Tonikiller10000/CH340G-FTDI-PROGRAMER/FtdiProgramer_Pictures/20230630_224606.jpg

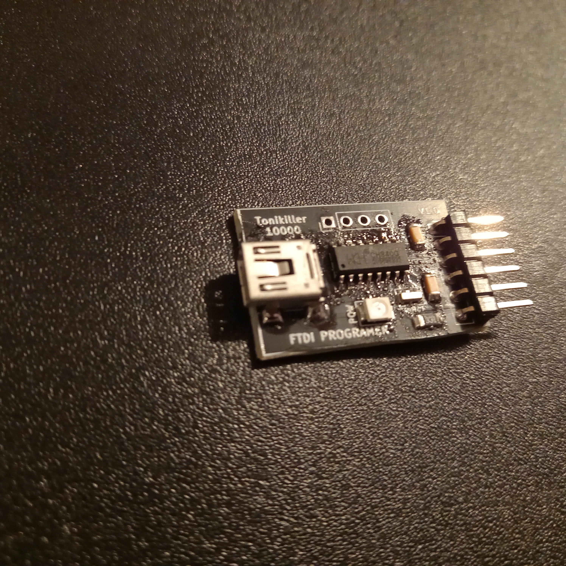
FtdiProgramer_Pictures/20230630_224606.jpg
