Tonikiller10000/CH340G-FTDI-PROGRAMER/FtdiProgramer_Pictures/20230701_103358.jpg

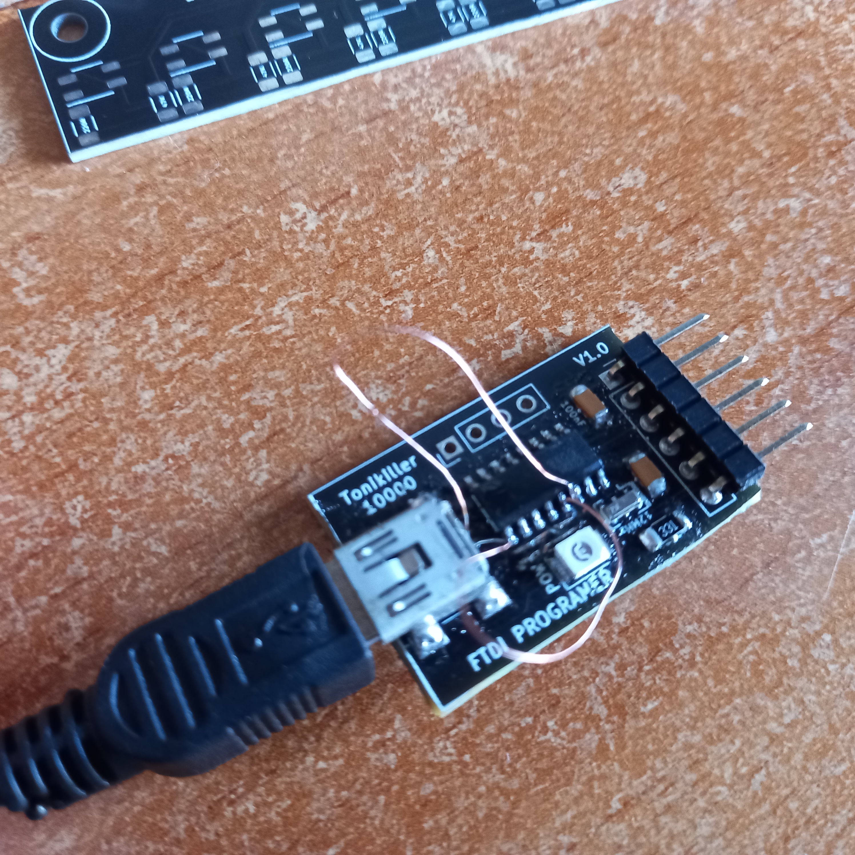
FtdiProgramer_Pictures/20230701_103358.jpg
