Tonikiller10000/CH340G-FTDI-PROGRAMER/FtdiProgramer_Pictures/20230709_143036.jpg

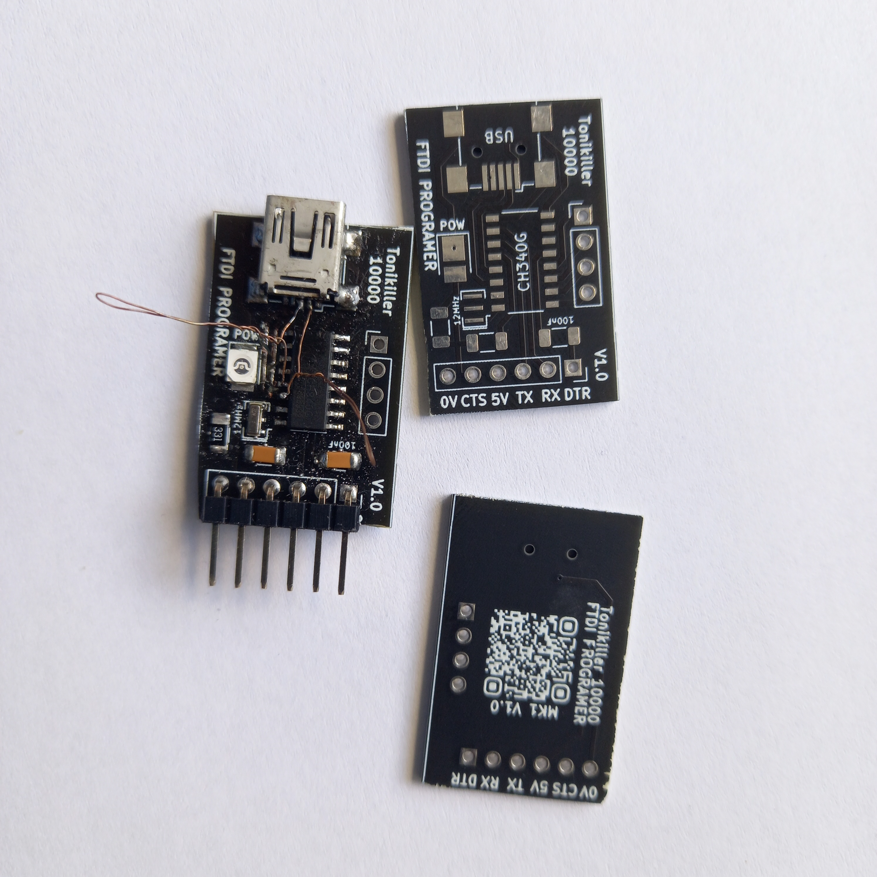
FtdiProgramer_Pictures/20230709_143036.jpg
