Tonikiller10000/CH340G-FTDI-PROGRAMER/FtdiProgramer_Pictures/20230709_143059.jpg

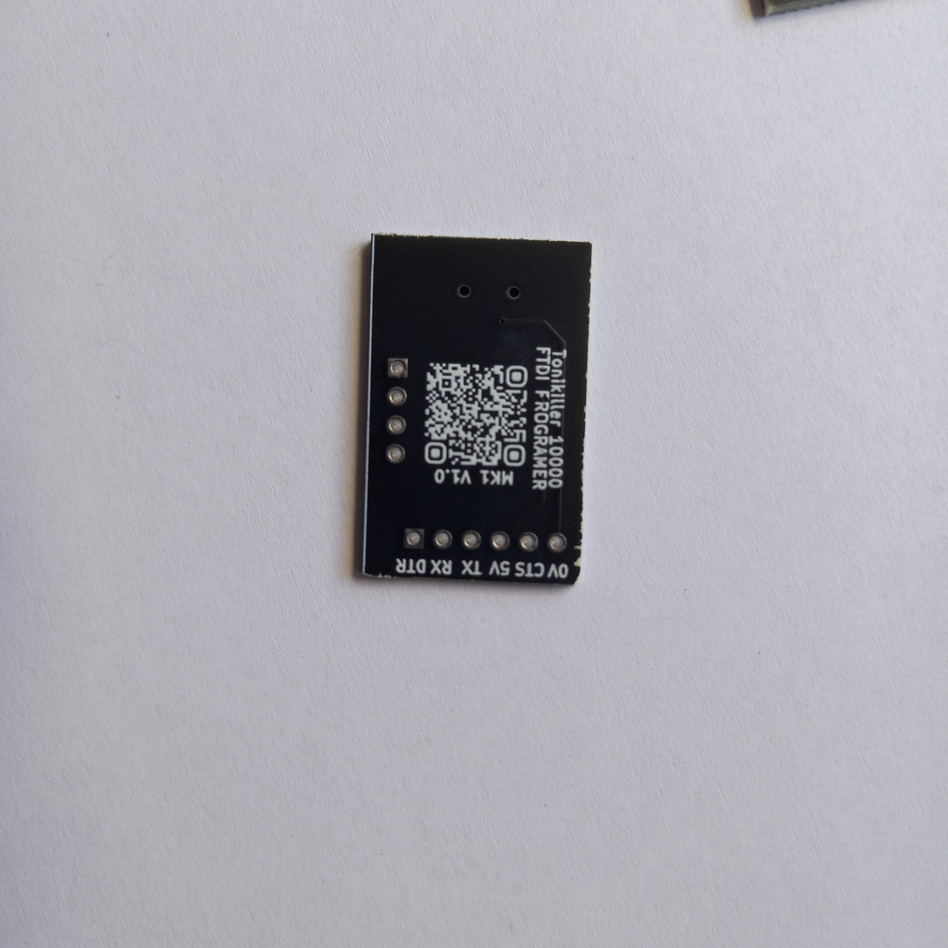
FtdiProgramer_Pictures/20230709_143059.jpg
