Tonikiller10000/CH340G-FTDI-PROGRAMER/FtdiProgramer_Pictures/20230709_143112.jpg

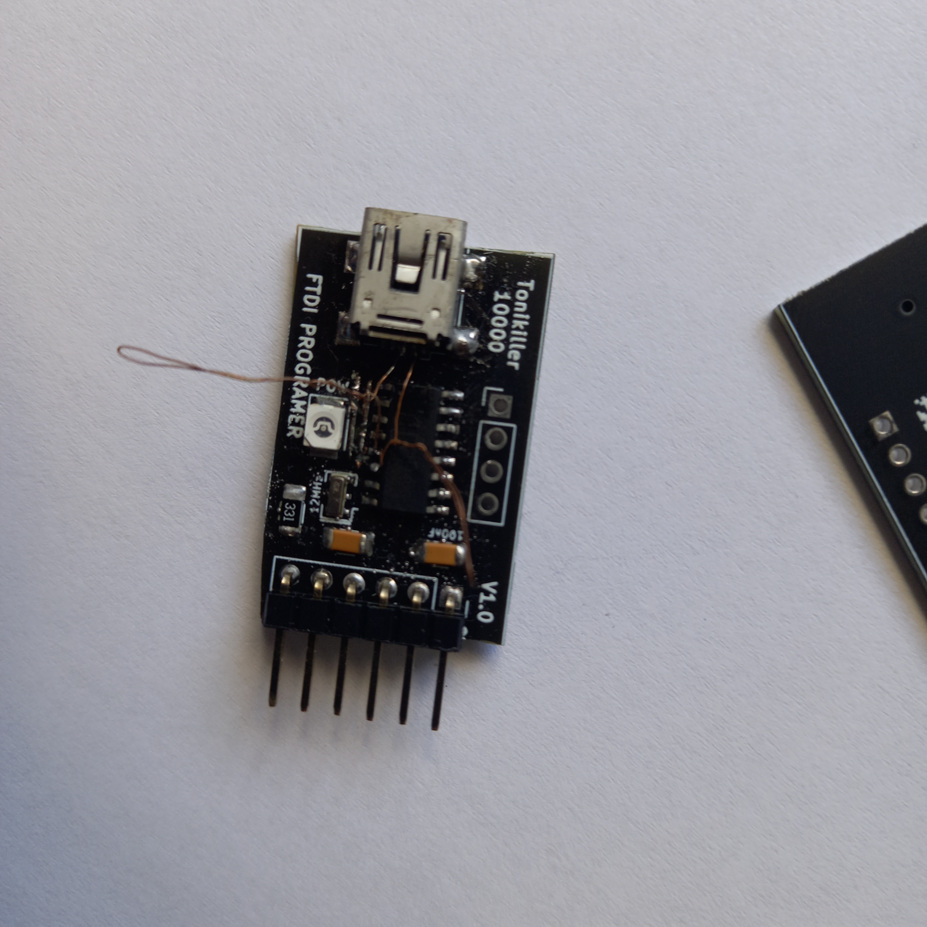
FtdiProgramer_Pictures/20230709_143112.jpg
