Tonikiller10000/CH340G-FTDI-PROGRAMER/FtdiProgramer_Pictures/20230920_141712.jpg

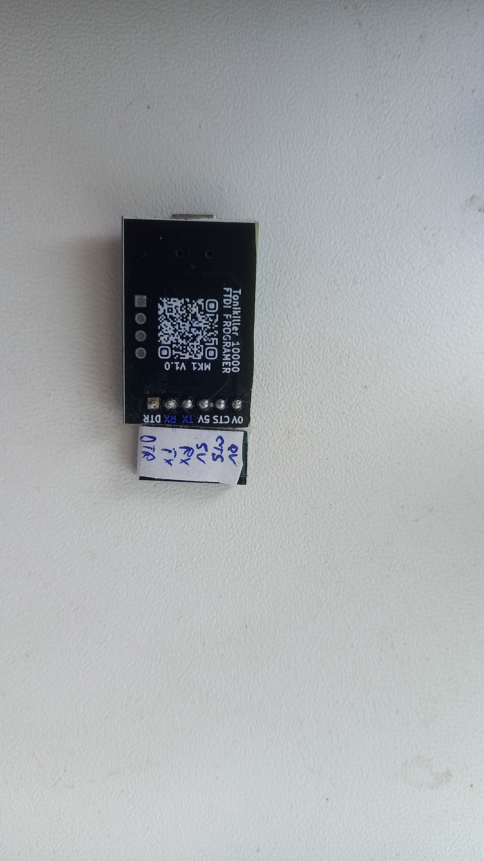
FtdiProgramer_Pictures/20230920_141712.jpg
