Tonikiller10000/CH340G-FTDI-PROGRAMER/FtdiProgramer_Pictures/b4.png

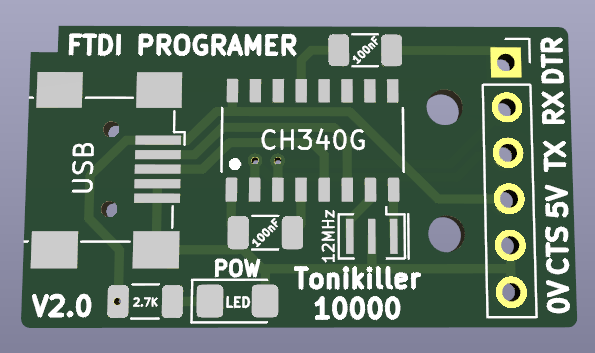
FtdiProgramer_Pictures/b4.png
