Tonikiller10000/CH340G-FTDI-PROGRAMER/FtdiProgramer_Pictures/fb.png

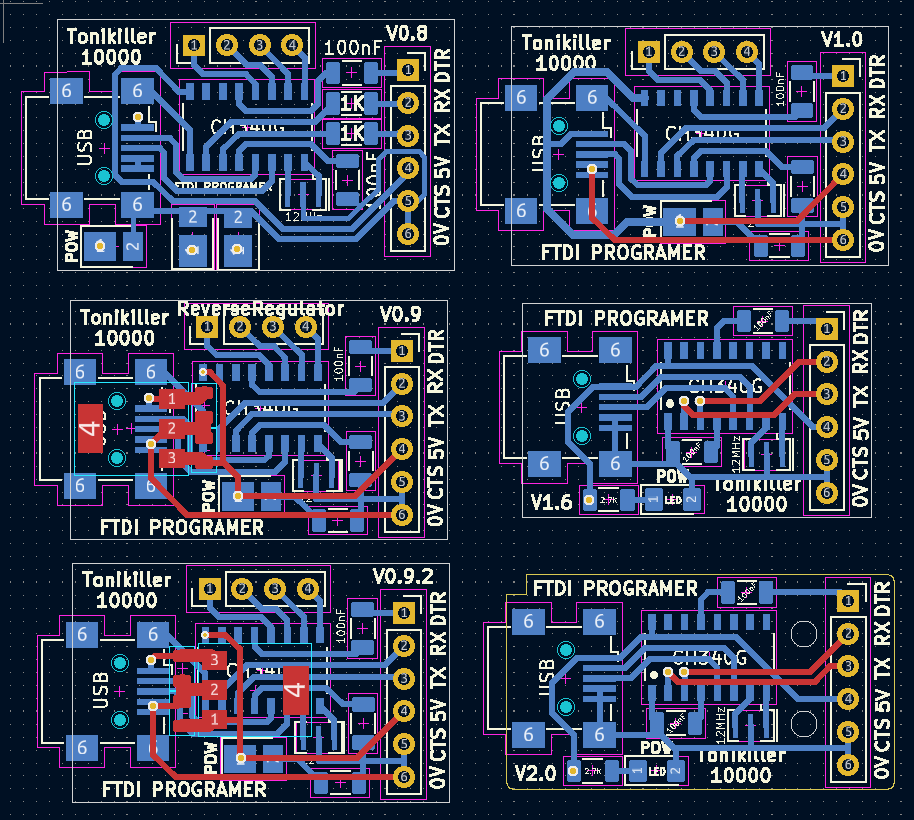
FtdiProgramer_Pictures/fb.png
