Tonikiller10000/CH340G-FTDI-PROGRAMER/FtdiProgramer_Pictures/ftd.png

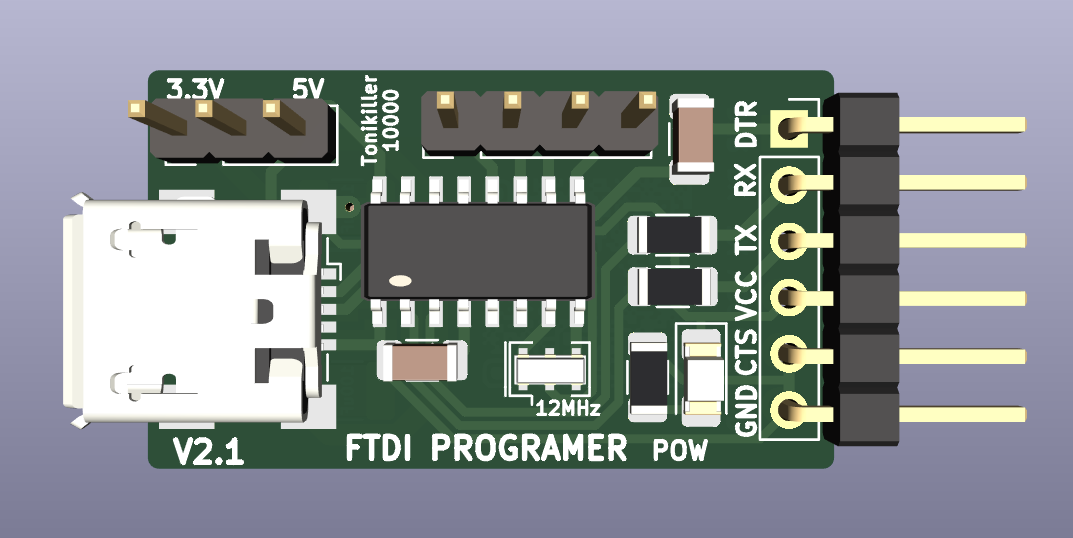
FtdiProgramer_Pictures/ftd.png
