Tonikiller10000/CH340G-FTDI-PROGRAMER/FtdiProgramer_Pictures/ss3.png

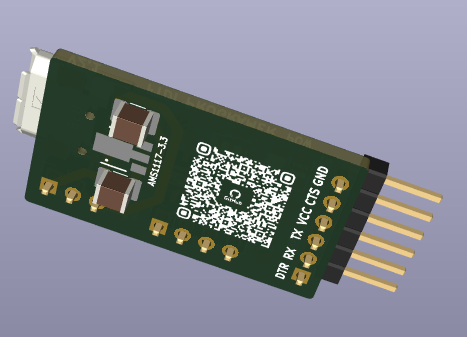
FtdiProgramer_Pictures/ss3.png
